Esser50K/PolarSketcher/models/EncoderHousingBottom.stl

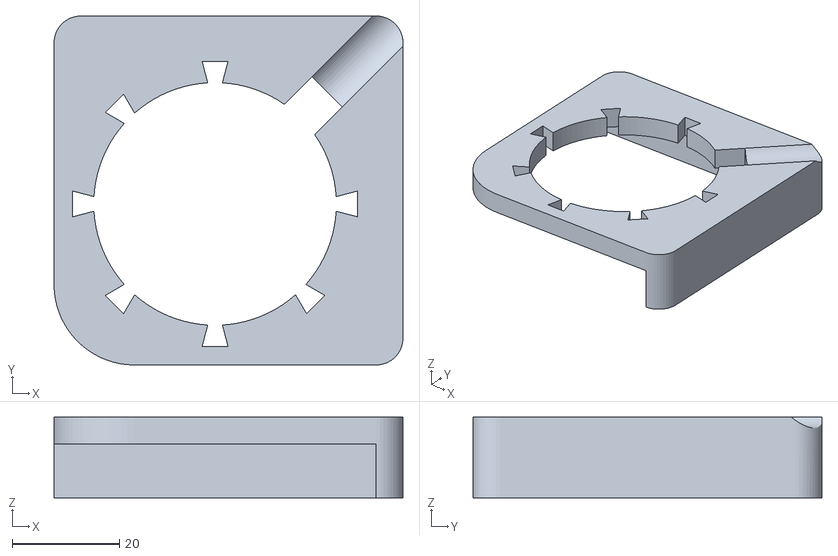
[picture p16: CAD file, 2023-11-26]
models/EncoderHousingBottom.stl
65.0 x 65.0 x 15.0
