Esser50K/PolarSketcher/models/bearingTop.stl

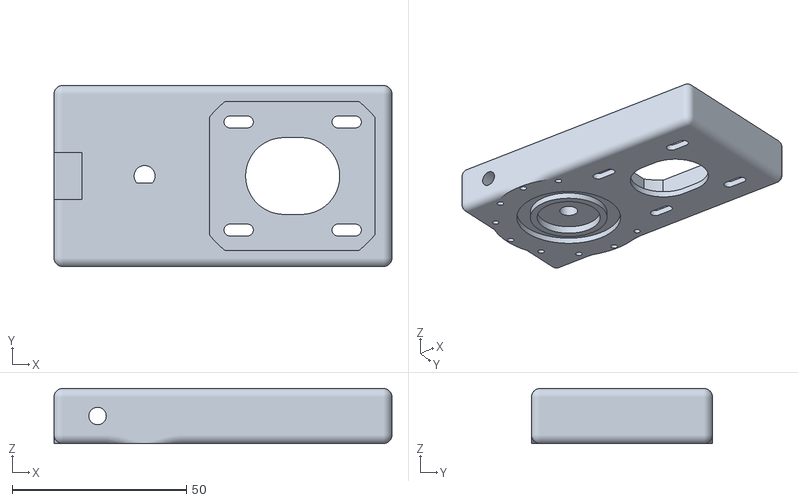
[picture p17: CAD file, 2023-11-26]
models/bearingTop.stl
97.0 x 52.0 x 15.8
